donzelot/hn70ap/src/bootloader_impl.c

/****************************************************************************
 * configs/hn70ap/src/bootloader_impl.c
 *
 *   Copyright (C) 2018 Sebastien Lorquet. All rights reserved.
 *   Author: Sebastien Lorquet <sebastien@lorquet.fr>
 *
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
 * 1. Redistributions of source code must retain the above copyright
 *    notice, this list of conditions and the following disclaimer.
 * 2. Redistributions in binary form must reproduce the above copyright
 *    notice, this list of conditions and the following disclaimer in
 *    the documentation and/or other materials provided with the
 *    distribution.
 * 3. Neither the name NuttX nor the names of its contributors may be
 *    used to endorse or promote products derived from this software
 *    without specific prior written permission.
 *
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
 ****************************************************************************/

/* Notes:
 *   - The clock is not changed, so we use the default, which is the 16 MHz HSI
 *     oscillator.
 */
#include "bootloader.h"
#include "bootloader_gpio.h"
#include "bootloader_uart.h"
#include "bootloader_spi.h"
#include "bootloader_intflash.h"
#include "bootloader_spiflash.h"
#include "bootloader_crc.h"
#include "bootloader_tlv.h"
#include "grxversion.h"

struct bootloader_update_header_s
{
  uint32_t size;
  uint32_t crc;
  uint8_t  sha[32];
  uint32_t sectorsize; /* Not really in the update header, but used to remember the ext flash sector size */
};

/* All text messages should be defined here instead of directly as parameters to
 * functions, because there is absolutely NO WAY to control which rodata section
 * is used to store litteral strings passed as parameters.
 * String messages must be declared as char arrays, NOT pointers.
 */
static const char hex[]          BOOTRODATA = "0123456789ABCDEF";
static const char CRLF[]         BOOTRODATA = "\r\n";
static const char STR_WELCOME[]  BOOTRODATA = "\r\n\r\n***** hn70ap_boot " GRXVERSION " *****\r\n";
static const char STR_NOFLASH[]  BOOTRODATA = "Flash not detected.\r\n";
static const char STR_BOOT[]     BOOTRODATA = "Starting OS.\r\n";
static const char STR_DOWNLOAD[] BOOTRODATA = "Download mode.\r\n";
static const char STR_NOUPDATE[] BOOTRODATA = "No update.\r\n";
static const char STR_BADHCRC[]  BOOTRODATA = "Bad Header CRC!\r\n";
static const char STR_DETECTED[] BOOTRODATA = "Update Detected...\r\n";
static const char STR_UPDATEOK[] BOOTRODATA = "Update Verified.\r\n";
static const char STR_ERASE[]    BOOTRODATA = "Erase:";
static const char STR_WRITE[]    BOOTRODATA = "Write:";
static const char STR_CHECK[]    BOOTRODATA = "Check:";
static const char STR_OK[]       BOOTRODATA = "OK\r\n";
static const char STR_FAIL[]     BOOTRODATA = "FAIL\r\n";
static const char STR_CLEANUP[]  BOOTRODATA = "Cleanup:";
static const char STR_STEP[]     BOOTRODATA = ".";

static uint8_t pgbuf[256] BOOTBSS;
static struct bootloader_update_header_s header BOOTBSS;

extern uint32_t _stext; /* Linker defined symbol that points to the start of the user software */

/* -------------------------------------------------------------------------- */
BOOTCODE void bootloader_memcpy(void *dest, void *src, uint32_t len)
{
  uint8_t *cdest = (uint8_t*)dest;
  uint8_t *csrc  = (uint8_t*)src;
  while(len > 0)
    {
      *cdest = *csrc;
      cdest++;
      csrc++;
      len--;
    }
}

/* -------------------------------------------------------------------------- */
/* Initialize all hardware needed by the bootloader */
BOOTCODE void bootloader_inithardware(void)
{
  /* Initialize UART4 */
  bootloader_gpio_init(UART4_TX);
  bootloader_gpio_init(UART4_RX);
  bootloader_uart_init(4);
  bootloader_uart_setbaud(4, 230400);

  /* Initialize SPI2 */
  bootloader_gpio_init(SPI2_MISO);
  bootloader_gpio_init(SPI2_MOSI);
  bootloader_gpio_init(SPI2_SCLK);
  bootloader_spi_init(2, SPI_MSBFIRST | SPI_MODE_0 | SPI_BAUDDIV_4); //Fastest speed OK without IRQs

  /* Initialize external flash */
  bootloader_gpio_init(FLASH_CS);
  bootloader_gpio_write(FLASH_CS, 1);
  bootloader_spiflash_reset(2);
  bootloader_spiflash_writeenable(2,true);
  bootloader_spiflash_globalunlock(2);
  bootloader_spiflash_writeenable(2,false);

  /* Initialize LEDs */
  bootloader_gpio_init(LED_HEARTBEAT);
  bootloader_gpio_init(LED_CPUACT);
  bootloader_gpio_init(LED_RED);
  bootloader_gpio_init(LED_ORANGE);

  bootloader_gpio_write(LED_RED      , 0);

  /* Initialize Button */
  bootloader_gpio_init(BUTTON);

  bootloader_intflash_init(FLASH_BLOCK_32);

  bootloader_uart_write_string(4, STR_WELCOME);
}

/* -------------------------------------------------------------------------- */
BOOTCODE void puthb(uint32_t uartid, uint8_t b)
{
  bootloader_uart_send(uartid, hex[b>> 4]);
  bootloader_uart_send(uartid, hex[b&0xf]);
}

/* -------------------------------------------------------------------------- */
/* Deinitialize all hardware that was initialized.
 * Specially important for SPI
 */
BOOTCODE void bootloader_stophardware(void)
{
  /* Stop internal LEDs, signalling starting of OS */
  bootloader_gpio_write(LED_RED      , 1);

  /* Reset the flash chip */
  bootloader_spiflash_reset(2);

  /* Disable SPI2, else NuttX wont properly initialize the SPI block */
  bootloader_spi_fini(2);

  /* Last string displayed before starting the OS */
  bootloader_uart_write_string(4, STR_BOOT);
}

/* -------------------------------------------------------------------------- */
/* Return the state of the on-board button. We need a small delay to ensure
 * that the debounce capacitor had time to discharge through the pin pullup. */
BOOTCODE bool bootloader_buttonpressed(void)
{
  volatile uint32_t delay;
  for(delay=0;delay<100000LU;delay++) {}
  return bootloader_gpio_read(BUTTON) == 0;
}

/* -------------------------------------------------------------------------- */
/* Read the contents of the external flash and determine if a valid
 * software image is present. If a check error happens, the update header page
 * is erased to avoid an infinite update failure loop, which will allow the
 * current OS to start.
 */
BOOTCODE bool bootloader_check(void)
{
  bool     success    = false;
  uint32_t crc;
  uint8_t  check;
  int i;
  uint8_t *ptr;
  uint32_t len;
  uint32_t page;
  uint32_t todo;

  /* Preparations. */
  bootloader_crc_init();

  /* Attempt to detect the flash */
  bootloader_spiflash_readjedec(2, pgbuf);
  
  if(pgbuf[0] == 0xBF && pgbuf[1] == 0x26 && pgbuf[2] == 0x43)
    {
      success           = true;
      header.sectorsize = 4096;
    }

  /* If the hardware is upgraded to support more flash devices, detect these
   * here. */

  if(!success)
    {
      bootloader_uart_write_string(4, STR_NOFLASH);
      return false;
    }

  /* Flash is there. Read the first page. */
  bootloader_spiflash_readpage(2, 0, pgbuf);

  /* Check for blank */
  check = 0xFF;
  for(i=0;i<256;i++)
    {
      //puthb(4, pgbuf[i]);
      check &= pgbuf[i];
    }
  if(check == 0xFF)
    {
      bootloader_uart_write_string(4, STR_NOUPDATE);
      return false;
    }

  /* Check CRC of header page */
  crc  = CRC32_INIT;
  crc  = bootloader_crc_do(crc, pgbuf+4, 252);
  crc ^= CRC32_MASK;
  crc ^= PEEK_U32BE(pgbuf);

  if(crc)
    {
      bootloader_uart_write_string(4, STR_BADHCRC);
      return false;
    }

  /* CRC is correct, means we're very likely to have an update */
  bootloader_uart_write_string(4, STR_DETECTED);

  /* Get update parameters */
  ptr = bootloader_tlv_find(pgbuf+4, 252, 0xC0, &len, 0);
  if(!ptr || len != 4)
    {
      bootloader_uart_write_string(4, STR_NOUPDATE);
      return false;
    }
  header.size = PEEK_U32BE(ptr);

  ptr = bootloader_tlv_find(pgbuf+4, 252, 0xC3, &len, 0);
  if(!ptr || len != 4)
    {
      bootloader_uart_write_string(4, STR_NOUPDATE);
      return false;
    }
  header.crc = PEEK_U32BE(ptr);

  ptr = bootloader_tlv_find(pgbuf+4, 252, 0xC3, &len, 0);
  if(ptr && len==32)
    {
      bootloader_memcpy(header.sha, ptr, 32);
    }

  /* Compute the CRC/SHA-256 of the image */
  page = 64;
  todo = header.size;
  crc  = CRC32_INIT;
  while(todo > 0)
    {
      bootloader_spiflash_readpage(2, page, pgbuf);
      crc = bootloader_crc_do(crc, pgbuf, (todo>256)?256:todo);
      todo -= (todo>256)?256:todo;
      page += 1;
    }
  crc ^= CRC32_MASK;

  if(crc == header.crc)
    {
      bootloader_uart_write_string(4, STR_UPDATEOK);
      return true;
    }

  return false;
}


/* -------------------------------------------------------------------------- */
/* Copy the firmware (supposed valid) from the external flash to the
 * internal stm32 flash. If we are interrupted anywhere in this proces, the
 * update (previously declared valid) can still be applied at next boot.
 */
BOOTCODE void bootloader_apply(void)
{
  uint32_t check;
  uint32_t todo;
  uint32_t page;
  volatile uint32_t *ptr;

  //return;

  /* Erase the internal flash */
  bootloader_uart_write_string(4, STR_ERASE);
  todo = (uint32_t)&_stext;
  check = 1;
  while(todo < ((uint32_t)&_stext + header.size) )
    {
      bootloader_uart_write_string(4, STR_STEP);
      todo += bootloader_intflash_erase(todo);
    }

  /* Blank check, word per word to save time */
  check = 0xFFFFFFFFL;
  ptr = &_stext;
  todo = header.size;
  todo = (todo+0x03) & ~0x03; //align on 4-byte boundary

  while(todo > 0)
    {
      check &= *ptr;
      ptr++;
      todo -= 4;
    }
  if(check != 0xFFFFFFFFL)
    {
      bootloader_uart_write_string(4, STR_FAIL);
      return;
    }
  bootloader_uart_write_string(4, STR_OK);

  /* Copy the update from spi flash to internal flash */
  bootloader_uart_write_string(4, STR_WRITE);
  ptr = &_stext;
  page = 64;
  todo = header.size;
  while(todo > 0)
    {
      int ret;
      bootloader_uart_write_string(4, STR_STEP);
      bootloader_spiflash_readpage(2, page, pgbuf);
      ret = bootloader_intflash_write((uint32_t)ptr, pgbuf, 256); //may write a bit of garbage at the end of flash
      if(ret != 0)
        {
          bootloader_uart_write_string(4, STR_FAIL);
          return;
        }
      todo -= (todo>256)?256:todo;
      page += 1;
      ptr += 256>>2;
    }
  bootloader_uart_write_string(4, STR_OK);

  /* Verify the contents of the internal flash */
  bootloader_uart_write_string(4, STR_CHECK);
  check = bootloader_crc_do(CRC32_INIT, (uint8_t*)&_stext, header.size);
  check ^= CRC32_MASK;
  if(check != header.crc)
    {
      bootloader_uart_write_string(4, STR_FAIL);
      return;
    }
  bootloader_uart_write_string(4, STR_OK);
}

/* -------------------------------------------------------------------------- */
BOOTCODE void bootloader_cleanup(void)
{
  bootloader_uart_write_string(4, STR_CLEANUP);
  uint32_t sect = 0;
  uint32_t todo = header.size + 16384;

  while(todo > 0)
    {
      bootloader_uart_write_string(4, STR_STEP);
      //puthb(4,sect>>8);puthb(4,sect);
      bootloader_spiflash_erase4ksector(2, sect);
      sect += 1;
      todo -= (todo > header.sectorsize) ? header.sectorsize : todo;
    }

  bootloader_uart_write_string(4, STR_OK);
  /* We can now erase the update header in the external flash. */
}

/* -------------------------------------------------------------------------- */
/* Handle a download protocol to fill the external flash from data received
 * through the UART. Protocol undefined yet.
 */
BOOTCODE void bootloader_download(void)
{
  bootloader_gpio_write(LED_RED      , 1);
  bootloader_gpio_write(LED_ORANGE   , 0);
  bootloader_uart_write_string(4, STR_DOWNLOAD);
}
